menckow/Zwitscher/src/MqttHandler.cpp

#include "MqttHandler.h"
#include "GlobalConfig.h"
#include "LedController.h"
#include "AudioEngine.h"
#include "WebManager.h"
#include <ArduinoJson.h>
#include <HTTPClient.h>
#include <HTTPUpdate.h>

#include "Audio.h"

extern AudioEngine audioEngine;

// Global instance 
MqttHandler mqttHandler;

// --- Object Methods ---

MqttHandler::MqttHandler() :
    mqttClient(espClient),
    mqttClientLamp(espClientLamp),
    lastMqttReconnectAttempt(0),
    lastLampMqttReconnectAttempt(0),
    mqttReconnectInterval(5000)
{
}

// --- v2 Helper -----------------------------------------------------------

std::vector<String> MqttHandler::getFamilies() {
    std::vector<String> result;
    String raw = config.family_ids;
    int start = 0;
    while (start <= (int)raw.length()) {
        int comma = raw.indexOf(',', start);
        String part = (comma < 0) ? raw.substring(start) : raw.substring(start, comma);
        part.trim();
        if (part.length() > 0) result.push_back(part);
        if (comma < 0) break;
        start = comma + 1;
    }
    return result;
}

String MqttHandler::getFamiliesJsonArray() {
    String out = "[";
    auto fams = getFamilies();
    for (size_t i = 0; i < fams.size(); i++) {
        if (i > 0) out += ",";
        out += "\"";
        out += fams[i];
        out += "\"";
    }
    out += "]";
    return out;
}

bool MqttHandler::isFamilySignalTopic(const char* topic) {
    for (auto& t : _familySignalTopics) {
        if (strcmp(topic, t.c_str()) == 0) return true;
    }
    return false;
}

String MqttHandler::getStatusTopicV2() {
    return "fl/device/" + config.mqtt_client_id + "/status";
}

void MqttHandler::publishStatusV2(const char* state, const char* extra) {
    String topic = getStatusTopicV2();
    String hexColor = config.friendlamp_color;
    if (!hexColor.equalsIgnoreCase("RAINBOW") && !hexColor.startsWith("#")) hexColor = "#" + hexColor;

    String payload;
    payload.reserve(256);
    payload += "{\"type\":\"" DEVICE_TYPE_BOX "\",";
    payload += "\"fw\":\"V"; payload += FW_VERSION; payload += "\",";
    payload += "\"state\":\""; payload += state; payload += "\",";
    payload += "\"color\":\""; payload += hexColor; payload += "\",";
    payload += "\"families\":"; payload += getFamiliesJsonArray();
    if (extra && *extra) {
        payload += ",\"info\":\""; payload += extra; payload += "\"";
    }
    payload += "}";

    if (config.homeassistant_mqtt_enabled && mqttClient.connected()) {
        mqttClient.publish(topic.c_str(), payload.c_str(), true);
    }
    if (config.friendlamp_mqtt_enabled && config.friendlamp_mqtt_server != "" && mqttClientLamp.connected()) {
        mqttClientLamp.publish(topic.c_str(), payload.c_str(), true);
    }
}

void MqttHandler::setupWifi() {
    if (!config.homeassistant_mqtt_enabled && !config.friendlamp_mqtt_enabled) {
        WiFi.mode(WIFI_OFF);
        Serial.println("All MQTT integrations disabled. WiFi is OFF.");
        return; 
    }

    if (config.wifi_ssid == "") {
        Serial.println("WiFi SSID not configured. Starting Config Portal.");
        webManager.startConfigPortal();
        return;
    }

    Serial.print("Connecting to WiFi SSID: ");
    Serial.println(config.wifi_ssid);

    WiFi.mode(WIFI_STA);
    WiFi.begin(config.wifi_ssid.c_str(), config.wifi_pass.c_str());

    unsigned long startAttemptTime = millis();
    while (WiFi.status() != WL_CONNECTED && millis() - startAttemptTime < 15000) {
        Serial.print(".");
        delay(500);
    }

    if (WiFi.status() != WL_CONNECTED) {
        ledCtrl.setBootStatusLeds(0, false);
        Serial.println("\nWiFi connection failed! Starting Config Portal.");
        WiFi.disconnect(true);
        webManager.startConfigPortal();
    } else {
        ledCtrl.setBootStatusLeds(0, true);
        Serial.println("\nWiFi connected!");
        Serial.print("IP address: ");
        Serial.println(WiFi.localIP());
        
        Serial.println("Starting NTP time sync...");
        configTzTime(config.timezone.c_str(), "pool.ntp.org", "time.nist.gov");
        
        publish(config.getTopicIp(), WiFi.localIP().toString(), true);

        Serial.println("----------------------------------------");
        Serial.println("Netzwerk & MQTT Status:");
        Serial.println("  WLAN (SSID): " + config.wifi_ssid);
        Serial.println("  IP Adresse:  " + WiFi.localIP().toString());
        if (config.homeassistant_mqtt_enabled) {
            Serial.println("  HA MQTT:     " + config.mqtt_server + ":" + String(config.mqtt_port));
        }
        if (config.friendlamp_mqtt_enabled && config.friendlamp_mqtt_server != "") {
            Serial.println("  Friend-MQTT: " + config.friendlamp_mqtt_server + ":" + String(config.friendlamp_mqtt_port));
        }
        Serial.println("----------------------------------------");
        
        webManager.setupWebServer();
    }
    
    // Config internal broker
    if (config.homeassistant_mqtt_enabled) {
        if (config.mqtt_server != "") {
            mqttClient.setServer(config.mqtt_server.c_str(), config.mqtt_port);
            mqttClient.setCallback(MqttHandler::staticMqttCallback);
            // Buffer auf 1024 Bytes fuer v2-JSON-Status (Default 256 zu klein).
            mqttClient.setBufferSize(1024);
            Serial.println("Internal MQTT Server configured.");
        } else {
             Serial.println("WARNING: Internal MQTT Server not configured, disabling HA integration.");
             config.homeassistant_mqtt_enabled = false;
        }
    }

    // Config Lamp broker
    if (config.friendlamp_mqtt_enabled && config.friendlamp_enabled && config.friendlamp_mqtt_server != "") {
        if (config.friendlamp_mqtt_tls_enabled) {
            if (config.mqtt_root_ca_content.length() > 20) {
                espClientSecureLamp.setCACert(config.mqtt_root_ca_content.c_str());
            } else {
                espClientSecureLamp.setInsecure();
            }
            mqttClientLamp.setClient(espClientSecureLamp);
        } else {
            mqttClientLamp.setClient(espClientLamp);
        }
        mqttClientLamp.setServer(config.friendlamp_mqtt_server.c_str(), config.friendlamp_mqtt_port);
        mqttClientLamp.setCallback(MqttHandler::staticMqttLampCallback);
        mqttClientLamp.setBufferSize(1024);
        Serial.println("Friendship Lamp MQTT Server configured.");
    }
}

void MqttHandler::internalMqttReconnect() {
    // v2: gemeinsame Topic-Vorbereitung
    String statusTopicV2 = getStatusTopicV2();
    String hexColor = config.friendlamp_color;
    if (!hexColor.equalsIgnoreCase("RAINBOW") && !hexColor.startsWith("#")) hexColor = "#" + hexColor;
    String lwtJson = String("{\"type\":\"" DEVICE_TYPE_BOX "\"") +
                     ",\"fw\":\"V" + FW_VERSION + "\"" +
                     ",\"state\":\"offline\"" +
                     ",\"color\":\"" + hexColor + "\"" +
                     ",\"families\":" + getFamiliesJsonArray() +
                     "}";

    // Familien-Signal-Topics einmal aufbauen (gleich fuer beide Broker)
    _familySignalTopics.clear();
    auto fams = getFamilies();
    for (auto& fam : fams) {
        _familySignalTopics.push_back("fl/family/" + fam + "/signal");
    }

    // Alte v1-Status-Topic einmalig leeren (Migration-Hygiene)
    String oldStatusTopic = "zwitscherbox/status/" + config.mqtt_client_id;

    if (config.homeassistant_mqtt_enabled && !mqttClient.connected() && (lastMqttReconnectAttempt == 0 || millis() - lastMqttReconnectAttempt > mqttReconnectInterval)) {
        lastMqttReconnectAttempt = millis();
        mqttClient.setClient(espClient);

        Serial.print("Attempting Internal (HA) MQTT connection...");
        bool connected = false;
        if (config.mqtt_user.length() > 0) {
             connected = mqttClient.connect(config.mqtt_client_id.c_str(), config.mqtt_user.c_str(), config.mqtt_pass.c_str(),
                                          statusTopicV2.c_str(), 1, true, lwtJson.c_str());
        } else {
             connected = mqttClient.connect(config.mqtt_client_id.c_str(), statusTopicV2.c_str(), 1, true, lwtJson.c_str());
        }

        static bool firstHaConnectAttempt = true;
        if (connected) {
            if (firstHaConnectAttempt) { ledCtrl.setBootStatusLeds(2, true); firstHaConnectAttempt = false; }
            Serial.println("connected");
            publish(config.getTopicIp(), WiFi.localIP().toString(), true);
            publish(config.getTopicStatus(), "Online", true);

            // --- v2 Subscribes ----------------------------------------
            for (auto& fam : fams) {
                String sig    = "fl/family/" + fam + "/signal";
                String otaFam = "fl/family/" + fam + "/update/trigger/" DEVICE_TYPE_BOX;
                mqttClient.subscribe(sig.c_str());
                mqttClient.subscribe(otaFam.c_str());
            }
            String otaPerDevice = "fl/device/" + config.mqtt_client_id + "/update/trigger";
            mqttClient.subscribe(otaPerDevice.c_str());
            mqttClient.subscribe("fl/_global/update/trigger/" DEVICE_TYPE_BOX);

            // v2 Status publishen + alten v1-Status-Topic einmalig leeren
            publishStatusV2("online");
            mqttClient.publish(oldStatusTopic.c_str(), "", true);

            Serial.printf("HA-MQTT v2 Subscribes aktiv. Familien: %u\n", (unsigned)fams.size());
            for (auto& fam : fams) Serial.println("    - " + fam);
        } else {
            if (firstHaConnectAttempt) { ledCtrl.setBootStatusLeds(2, false); firstHaConnectAttempt = false; }
            Serial.print("failed, rc=");
            Serial.print(mqttClient.state());
            Serial.println(" try again later");
        }
    }

    if (config.friendlamp_mqtt_enabled && config.friendlamp_enabled && config.friendlamp_mqtt_server != "" && !mqttClientLamp.connected()) {
        if (lastLampMqttReconnectAttempt == 0 || millis() - lastLampMqttReconnectAttempt > mqttReconnectInterval) {
            lastLampMqttReconnectAttempt = millis();
            Serial.print("Attempting Lamp MQTT connection...");
            bool connected = false;

            String lampClientId = config.mqtt_client_id + "_Lamp";

            if (config.friendlamp_mqtt_user.length() > 0) {
                 connected = mqttClientLamp.connect(lampClientId.c_str(), config.friendlamp_mqtt_user.c_str(), config.friendlamp_mqtt_pass.c_str(),
                                              statusTopicV2.c_str(), 1, true, lwtJson.c_str());
            } else {
                 connected = mqttClientLamp.connect(lampClientId.c_str(), statusTopicV2.c_str(), 1, true, lwtJson.c_str());
            }

            static bool firstLampConnectAttempt = true;
            if (connected) {
                if (firstLampConnectAttempt) { ledCtrl.setBootStatusLeds(3, true); firstLampConnectAttempt = false; }
                Serial.println("connected");

                // --- v2 Subscribes auf Friendlamp-Broker ------------------
                for (auto& fam : fams) {
                    String sig    = "fl/family/" + fam + "/signal";
                    String otaFam = "fl/family/" + fam + "/update/trigger/" DEVICE_TYPE_BOX;
                    mqttClientLamp.subscribe(sig.c_str());
                    mqttClientLamp.subscribe(otaFam.c_str());
                }
                String otaPerDeviceLamp = "fl/device/" + config.mqtt_client_id + "/update/trigger";
                mqttClientLamp.subscribe(otaPerDeviceLamp.c_str());
                mqttClientLamp.subscribe("fl/_global/update/trigger/" DEVICE_TYPE_BOX);

                publishStatusV2("online");
                mqttClientLamp.publish(oldStatusTopic.c_str(), "", true);

                Serial.printf("Friendlamp-MQTT v2 Subscribes aktiv. Familien: %u\n", (unsigned)fams.size());
            } else {
                if (firstLampConnectAttempt) { ledCtrl.setBootStatusLeds(3, false); firstLampConnectAttempt = false; }
                Serial.print("failed, rc=");
                Serial.print(mqttClientLamp.state());
                Serial.println(" try again later");
            }
        }
    }
}

void MqttHandler::update() {
    if (config.homeassistant_mqtt_enabled || config.friendlamp_mqtt_enabled) {
        if (WiFi.status() == WL_CONNECTED) {
            internalMqttReconnect(); 
            
            if (config.homeassistant_mqtt_enabled && mqttClient.connected()) {
                mqttClient.loop();
            }
            if (config.friendlamp_mqtt_enabled && config.friendlamp_enabled && config.friendlamp_mqtt_server != "" && mqttClientLamp.connected()) {
                mqttClientLamp.loop(); 
            }
        } else {
            static unsigned long lastWifiCheck = 0;
            if (millis() - lastWifiCheck > 30000) { 
                Serial.println("WiFi disconnected. Attempting reconnect...");
                WiFi.disconnect();
                WiFi.reconnect();
                lastWifiCheck = millis();
            }
        }
    }
}

void MqttHandler::forceReconnect() {
    internalMqttReconnect();
}

void MqttHandler::publish(const String& topic, const String& payload, bool retain) {
    if (!config.homeassistant_mqtt_enabled || !mqttClient.connected()) return;
    mqttClient.publish(topic.c_str(), payload.c_str(), retain);
}

void MqttHandler::publishLamp(const String& topic, const String& payload, bool retain) {
    if (!config.friendlamp_mqtt_enabled || !config.friendlamp_enabled) return;
    
    if (config.friendlamp_mqtt_server != "") {
        if (mqttClientLamp.connected()) {
            mqttClientLamp.publish(topic.c_str(), payload.c_str(), retain);
        }
    } else {
        if (config.homeassistant_mqtt_enabled && mqttClient.connected()) {
            mqttClient.publish(topic.c_str(), payload.c_str(), retain);
        }
    }
}

void MqttHandler::handleFreundschaftMessage(String payload) {
    if (isQuietTime()) {
        Serial.println("--> handleFreundschaftMessage: Ignored message due to active Quiet Time (Do Not Disturb).");
        return;
    }

    Serial.println("--> handleFreundschaftMessage: Received " + payload);

    String colorStr = "";
    String effect = "fade";
    long duration = 30000;
    String senderId = "";
    uint32_t parsedColor = 0;
    bool hasLegacyRGB = false;

    JsonDocument doc;
    DeserializationError error = deserializeJson(doc, payload);
    
    if (!error && !doc["client_id"].isNull()) {
        senderId = doc["client_id"] | "";
        colorStr = doc["color"] | "";
        effect = doc["effect"] | "fade";
        duration = doc["duration"] | 30000;
    } else {
        if (payload.equalsIgnoreCase("RAINBOW")) {
            colorStr = "RAINBOW";
        } else {
            int firstComma = payload.indexOf(',');
            int secondComma = payload.lastIndexOf(',');
            if (firstComma != -1 && secondComma != -1 && firstComma != secondComma) {
                int r = payload.substring(0, firstComma).toInt();
                int g = payload.substring(firstComma + 1, secondComma).toInt();
                int b = payload.substring(secondComma + 1).toInt();
                parsedColor = Adafruit_NeoPixel::Color(r, g, b);
                hasLegacyRGB = true;
            } else {
                int colonPos = payload.indexOf(':');
                if (colonPos != -1) {
                    senderId = payload.substring(0, colonPos);
                    colorStr = payload.substring(colonPos + 1);
                } else {
                    colorStr = payload;
                }
            }
        }
    }

    if (senderId.length() > 0 && senderId == config.mqtt_client_id) {
        Serial.println("--> handleFreundschaftMessage: Ignored own message.");
        return;
    }

    if (colorStr.startsWith("#")) colorStr = colorStr.substring(1);
    bool isRainbow = effect.equalsIgnoreCase("rainbow") || colorStr.equalsIgnoreCase("RAINBOW");
    bool isBlink = effect.equalsIgnoreCase("blink");
    
    uint32_t finalColor = 0;
    if (isRainbow) {
        finalColor = 0;
    } else if (hasLegacyRGB) {
        finalColor = parsedColor;
    } else {
        finalColor = strtol(colorStr.c_str(), NULL, 16);
    }
    
    Serial.printf("--> handleFreundschaftMessage: Activated 3rd LED mode. final value: %u\n", finalColor);

    ledCtrl.startFadeIn(finalColor, 1, isRainbow, isBlink);
    ledCtrl.ledTimeout = millis() + duration;
    ledCtrl.ledActive = true; 
}

void MqttHandler::performOtaUpdate(const char* url, const char* version, const char* md5) {
    Serial.println("OTA Update Prozess gestartet...");
    Serial.printf("Update-URL: %s\n", url);

    if (audioEngine.getState() != PlaybackState::IDLE && audioEngine.getState() != PlaybackState::STANDBY && audioEngine.getState() != PlaybackState::INITIALIZING) {
        audioEngine.stopPlayback();
    }

    String updateStatusTopic = "fl/device/" + config.mqtt_client_id + "/update/status";
    String startMsg = "Updating to " + String(version);
    publishStatusV2("updating", startMsg.c_str());
    if (config.homeassistant_mqtt_enabled && mqttClient.connected()) {
        mqttClient.publish(updateStatusTopic.c_str(), startMsg.c_str());
    }
    if (config.friendlamp_mqtt_enabled && config.friendlamp_mqtt_server != "" && mqttClientLamp.connected()) {
        mqttClientLamp.publish(updateStatusTopic.c_str(), startMsg.c_str());
    }

    bool isHttps = String(url).startsWith("https://");

    if (config.friendlamp_enabled) {
        ledCtrl.setSolidColor(0x0000FF); // Blue solid
    }

    httpUpdate.setFollowRedirects(HTTPC_FORCE_FOLLOW_REDIRECTS);

    if (md5 == nullptr || strlen(md5) != 32) {
        String errorMsg = String(config.mqtt_client_id) + " - Update failed: Invalid or missing MD5 hash (must be 32 characters)";
        Serial.println(errorMsg);
        publishStatusV2("error", errorMsg.c_str());
        if (config.homeassistant_mqtt_enabled && mqttClient.connected()) mqttClient.publish(updateStatusTopic.c_str(), errorMsg.c_str(), false);
        if (config.friendlamp_mqtt_enabled && config.friendlamp_mqtt_server != "" && mqttClientLamp.connected()) mqttClientLamp.publish(updateStatusTopic.c_str(), errorMsg.c_str(), false);

        if (config.friendlamp_enabled) {
            ledCtrl.setSolidColor(0xFF0000); // Red
            delay(2000);
            ledCtrl.turnOff();
        }

        // Revert status so dashboard recovers
        delay(3000);
        publishStatusV2("online");
        return;
    }

    Serial.printf("Sicherheits-Check: MD5 Hash Validierung aktiviert (%s)\n", md5);
    httpUpdate.setMD5sum(md5);

    httpUpdate.onProgress([this, updateStatusTopic](int cur, int total) {
        static int lastPercent = -1;
        int percent = (cur * 100) / total;
        if (percent % 10 == 0 && percent != lastPercent) {
            lastPercent = percent;
            Serial.printf("OTA Download: %d%%\n", percent);

            if (config.friendlamp_enabled) {
                ledCtrl.setOtaProgress(percent);
            }

            String progMsg = "Updating (" + String(percent) + "%)";
            publishStatusV2("updating", progMsg.c_str());
            if (config.homeassistant_mqtt_enabled && mqttClient.connected()) {
                mqttClient.publish(updateStatusTopic.c_str(), progMsg.c_str());
            }
            if (config.friendlamp_mqtt_enabled && config.friendlamp_mqtt_server != "" && mqttClientLamp.connected()) {
                mqttClientLamp.publish(updateStatusTopic.c_str(), progMsg.c_str());
            }
        }
    });

    t_httpUpdate_return ret;
    if (isHttps) {
        WiFiClientSecure secureClient;
        secureClient.setInsecure();
        ret = httpUpdate.update(secureClient, url);
    } else {
        WiFiClient insecureClient;
        ret = httpUpdate.update(insecureClient, url);
    }

    switch (ret) {
        case HTTP_UPDATE_FAILED: {
            String errorMsg = String(config.mqtt_client_id) + " - Update failed: " + httpUpdate.getLastErrorString();
            Serial.println(errorMsg);
            publishStatusV2("error", errorMsg.c_str());
            if (config.homeassistant_mqtt_enabled && mqttClient.connected()) mqttClient.publish(updateStatusTopic.c_str(), errorMsg.c_str(), false);
            if (config.friendlamp_mqtt_enabled && config.friendlamp_mqtt_server != "" && mqttClientLamp.connected()) mqttClientLamp.publish(updateStatusTopic.c_str(), errorMsg.c_str(), false);
            if (config.friendlamp_enabled) {
                ledCtrl.setSolidColor(0xFF0000); // Red
                delay(2000);
                ledCtrl.turnOff();
            }

            // Revert to stable status after letting the error display briefly
            delay(3000);
            publishStatusV2("online");
            break;
        }
        case HTTP_UPDATE_NO_UPDATES:
            Serial.println("Keine Updates verfügbar.");
            if (config.friendlamp_enabled) {
                ledCtrl.turnOff();
            }
            break;
        case HTTP_UPDATE_OK: {
            Serial.println("Update erfolgreich! ESP32 startet neu...");
            String okMsg = String(config.mqtt_client_id) + " - Success! Rebooting...";
            publishStatusV2("updating", okMsg.c_str());
            if (config.homeassistant_mqtt_enabled && mqttClient.connected()) mqttClient.publish(updateStatusTopic.c_str(), okMsg.c_str(), false);
            if (config.friendlamp_mqtt_enabled && config.friendlamp_mqtt_server != "" && mqttClientLamp.connected()) mqttClientLamp.publish(updateStatusTopic.c_str(), okMsg.c_str(), false);
            if (config.friendlamp_enabled) {
                ledCtrl.turnOff();
            }
            delay(1000);
            ESP.restart();
            break;
        }
    }
}

void MqttHandler::handleLampCallback(char* topic, byte* payload, unsigned int length) {
    String message = "";
    for (unsigned int i = 0; i < length; i++) {
        message += (char)payload[i];
    }
    Serial.printf("MQTT Received [%s]: %s\n", topic, message.c_str());

    time_t now = time(nullptr);

    // --- v2 OTA-Topics --------------------------------------------------
    String otaPerDevice = "fl/device/" + config.mqtt_client_id + "/update/trigger";
    String otaGlobalBox = String("fl/_global/update/trigger/") + DEVICE_TYPE_BOX;
    bool isPerDeviceOta = (strcmp(topic, otaPerDevice.c_str()) == 0);
    bool isGlobalOta    = (strcmp(topic, otaGlobalBox.c_str()) == 0);
    bool isFamilyOta    = false;
    {
        String tStr(topic);
        String prefix = "fl/family/";
        String suffix = String("/update/trigger/") + DEVICE_TYPE_BOX;
        if (tStr.startsWith(prefix) && tStr.endsWith(suffix)) {
            isFamilyOta = true;
        }
    }

    if (isPerDeviceOta || isGlobalOta || isFamilyOta) {
        JsonDocument doc;
        DeserializationError error = deserializeJson(doc, message);
        if (error) {
            Serial.println("OTA: payload nicht parsebar");
            return;
        }

        // Defense-in-depth: target_type-Check
        if (!doc["target_type"].isNull()) {
            const char* tt = doc["target_type"];
            if (tt && strcmp(tt, DEVICE_TYPE_BOX) != 0) {
                Serial.printf("OTA: ignoriert (target_type=%s passt nicht zu %s)\n", tt, DEVICE_TYPE_BOX);
                return;
            }
        }

        const char* url = doc["url"] | "";
        const char* version = doc["version"] | "";
        const char* md5 = doc["md5"] | "";
        if (strlen(url) > 0 && strlen(version) > 0) {
            if (strcmp(version, FW_VERSION) != 0) {
                performOtaUpdate(url, version, md5);
            } else {
                String upStatus = "fl/device/" + config.mqtt_client_id + "/update/status";
                String okMsg = "V" + String(FW_VERSION) + ":" + String(config.mqtt_client_id) + " - Already up to date";
                if (config.homeassistant_mqtt_enabled && mqttClient.connected()) mqttClient.publish(upStatus.c_str(), okMsg.c_str(), false);
                if (config.friendlamp_mqtt_enabled && config.friendlamp_mqtt_server != "" && mqttClientLamp.connected()) mqttClientLamp.publish(upStatus.c_str(), okMsg.c_str(), false);
            }
        }
        return;
    }

    // --- v2 Familien-Signal-Topic? --------------------------------------
    if (!isFamilySignalTopic(topic)) return;

    // Ruhemodus
    if (isQuietTime()) {
        Serial.println("Signal ignoriert: Ruhemodus aktiv");
        return;
    }

    JsonDocument doc;
    DeserializationError error = deserializeJson(doc, message);
    if (error) {
        Serial.println("Signal ignoriert: payload nicht parsebar");
        return;
    }

    // NTP-Schutz: Alter pruefen wenn ts mitkommt
    if (!doc["ts"].isNull()) {
        time_t msgTs = doc["ts"] | 0;
        if (now > 0 && msgTs > 0) {
            long age = (long)now - (long)msgTs;
            if (abs(age) > 60) {
                Serial.printf("Signal ignoriert: Veraltet (Alter: %lds)\n", age);
                return;
            }
        }
    }

    // Self-Filter (wichtig bei Mehrfachmitgliedschaft)
    String senderId = doc["client_id"] | "";
    if (senderId.length() > 0 && senderId == config.mqtt_client_id) {
        Serial.println("Signal ignoriert: eigene Nachricht");
        return;
    }

    String colorStr = doc["color"] | "";
    String effect = doc["effect"] | "fade";
    long duration = doc["duration"] | 30000;
    String senderType = doc["sender_type"] | "";  // "lamp" oder "box" (oder leer = v2 ohne Typ)

    if (colorStr.startsWith("#")) colorStr = colorStr.substring(1);
    bool isRainbow = effect.equalsIgnoreCase("rainbow") || colorStr.equalsIgnoreCase("RAINBOW");
    bool isBlink   = effect.equalsIgnoreCase("blink");
    ledCtrl.currentLedColor = isRainbow ? 0 : strtol(colorStr.c_str(), NULL, 16);
    ledCtrl.ledTimeout = millis() + duration;
    ledCtrl.ledActive = true;

    // ringMode=1 aktiviert den Komplementaer-LED-Modus (siehe FadeEffect),
    // damit der Empfaenger optisch erkennt, dass das Signal von einer Lampe stammt.
    int ringMode = senderType.equalsIgnoreCase("lamp") ? 1 : 0;
    if (config.friendlamp_enabled) {
        ledCtrl.startFadeIn(ledCtrl.currentLedColor, ringMode, isRainbow, isBlink);
    }
}

void MqttHandler::handleStandardCallback(char* topic, byte* payload, unsigned int length) {
    handleLampCallback(topic, payload, length);
}

// Static Bridges
void MqttHandler::staticMqttCallback(char* topic, byte* payload, unsigned int length) {
    mqttHandler.handleStandardCallback(topic, payload, length);
}

void MqttHandler::staticMqttLampCallback(char* topic, byte* payload, unsigned int length) {
    mqttHandler.handleLampCallback(topic, payload, length);
}

bool MqttHandler::isQuietTime() {
    if (!config.quiet_time_enabled) return false;
    
    struct tm timeinfo;
    if (!getLocalTime(&timeinfo, 50)) {
        return false; // Time not set yet, don't drop messages
    }
    
    int startH = config.quiet_time_start.substring(0, 2).toInt();
    int startM = config.quiet_time_start.substring(3, 5).toInt();
    int endH = config.quiet_time_end.substring(0, 2).toInt();
    int endM = config.quiet_time_end.substring(3, 5).toInt();
    
    int currentMins = timeinfo.tm_hour * 60 + timeinfo.tm_min;
    int startMins = startH * 60 + startM;
    int endMins = endH * 60 + endM;
    
    if (startMins <= endMins) {
        return (currentMins >= startMins && currentMins < endMins);
    } else {
        return (currentMins >= startMins || currentMins < endMins); // wraps around midnight
    }
}
