menckow/Zwitscher/config.example.txt

# ------------------------------------------------------------------------
# Zwitscher - Configuration File (config.txt)
# ------------------------------------------------------------------------
# 1. Speichere diese Datei direkt in das Hauptverzeichnis (Root) deiner SD-Karte.
# 2. Passe die Platzhalter (ohne Leerzeichen nach dem "=") an dein Netzwerk an.
# ------------------------------------------------------------------------

# --- 1. MQTT-Aktivierung ---
# Setze diesen Wert auf 1, um die Status-Übermittlung an deinen internen
# MQTT Broker (z.B. Home Assistant) zu aktivieren.
MQTT_INTEGRATION=0

# Setze diesen Wert auf 1, um die Freundschaftslampen-Funktion über MQTT
# zu aktivieren. Dies kann der interne oder ein öffentlicher Broker sein.
FRIENDLAMP_MQTT_INTEGRATION=0

# Hinweis: Wenn beide obigen Werte auf 0 stehen, bleibt das Gerät offline (kein WLAN).

# --- 2. WLAN (WiFi) Einstellungen ---
# Erforderlich, wenn eine der MQTT-Integrationen aktiviert ist.
WIFI_SSID=DeinWLANNetzwerkName
WIFI_PASS=DeinWLANPasswort

# --- 3. Interner MQTT Broker (für Home Assistant) ---
# Gib hier die IP-Adresse deines MQTT Brokers (z.B. Raspberry Pi / Home Assistant) ein.
MQTT_SERVER=DeinMQTTServer
MQTT_PORT=1883

# (Optional) Benutzername und Passwort für den internen MQTT Broker. 
MQTT_USER=mqtt_benutzer
MQTT_PASS=mqtt_passwort

# --- 4. MQTT Topics und Client-Namen ---
# Eindeutige ID des Players im Netzwerk
MQTT_CLIENT_ID=ESP32_AudioPlayer

# Das Basis-Topic für alle Status-Meldungen an Home Assistant
# (z. B. audioplayer/status, audioplayer/playing, audioplayer/volume)
MQTT_BASE_TOPIC=InternesBaseTopic

# --- 5. Freundschaftslampe (RGB LED Ring) ---
# Schaltet die LED-Ring-Hardware an (1) oder aus (0).
# FRIENDLAMP_MQTT_INTEGRATION muss ebenfalls auf 1 sein, damit dies funktioniert.
FRIENDLAMP_ENABLE=1

# Feste Sende-Farbe für DIESE Box im Hex-Format (z. B. FF0000 = Rot, 00FF00 = Grün, 0000FF = Blau)
FRIENDLAMP_COLOR=0000FF

# Topic über das die Lampen kommunizieren (muss auf allen Boxen gleich sein!)
FRIENDLAMP_TOPIC=zwitscherbox/friendlamp

# Aktiviert den Fade-Effekt für die LEDs (1 = an, 0 = aus)
LED_FADE_EFFECT=1

# Dauer für das Ein- und Ausblenden in Millisekunden (z.B. 1000 = 1 Sekunde)
LED_FADE_DURATION=1000

# Helligkeit des LED-Rings (Werte von 0 bis 255)
LED_BRIGHTNESS=100

# --- Externer Broker für die Freundschaftslampe (Optional) ---
# Wenn diese Felder leer bleiben, wird automatisch der interne Broker verwendet
# (falls MQTT_INTEGRATION=1 gesetzt ist).
FRIENDLAMP_MQTT_SERVER=test.mosquitto.org
FRIENDLAMP_MQTT_PORT=1883
FRIENDLAMP_MQTT_USER=
FRIENDLAMP_MQTT_PASS=

# --- 6. TLS-Verschlüsselung für externen Friendlamp Broker ---
# Setze diesen Wert auf 1, um TLS für die Freundschaftslampen MQTT-Verbindung zu aktivieren.
# Der Home Assistant MQTT-Server (intern) bleibt immer unverschlüsselt.
# Der Port für den Friendlamp Broker muss bei TLS meist auf 8883 geändert werden.
FRIENDLAMP_MQTT_TLS_ENABLED=0

# Das Root-Zertifikat für die TLS-Validierung.
# Wird nur verwendet, wenn FRIENDLAMP_MQTT_TLS_ENABLED=1 ist.
BEGIN_CERT
-----BEGIN CERTIFICATE-----
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
-----END CERTIFICATE-----
END_CERT
